Flygonial/The-Gryphon-Foam-Dart-Blaster/Gryphon Takedown/Magwell TKD/Magwell (Grip) TKD.stl

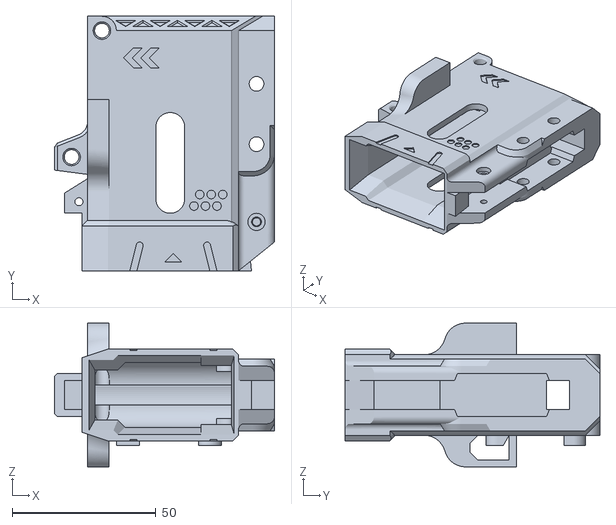
[picture p6: CAD file, 2022-05-22]
Gryphon Takedown/Magwell TKD/Magwell (Grip) TKD.stl
76.5 x 88.5 x 50.0
