Flygonial/The-Gryphon-Foam-Dart-Blaster/Gryphon Takedown/Other TKD Components/Pusher TKD.stl

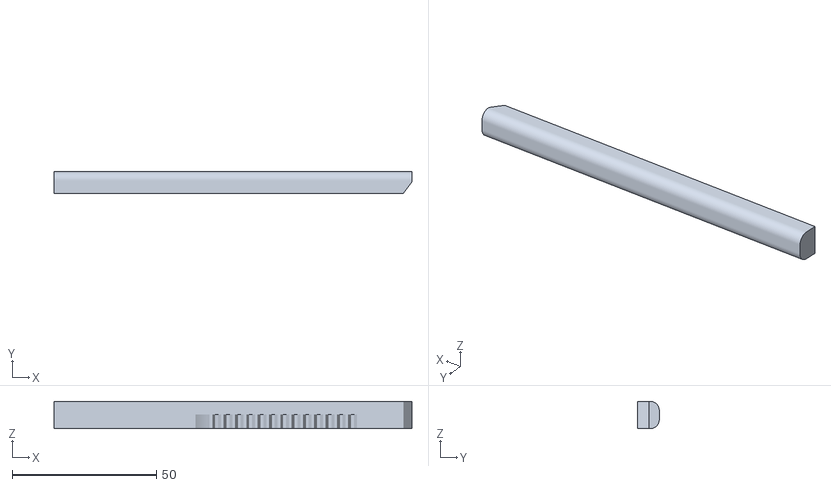
[picture p7: CAD file, 2022-05-22]
Gryphon Takedown/Other TKD Components/Pusher TKD.stl
124.1 x 7.50 x 9.50
