Flygonial/The-Gryphon-Foam-Dart-Blaster/Gryphon Takedown/Picatinny TKD/2S Bottom Picatinny TKD.stl

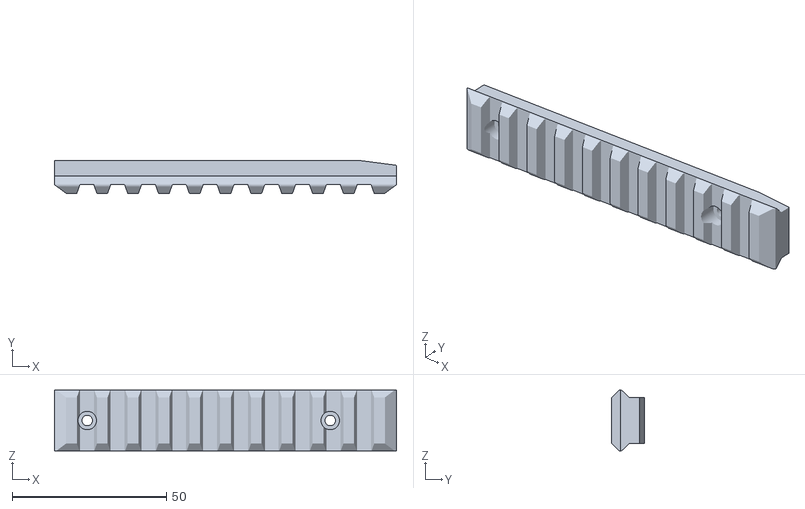
[picture p8: CAD file, 2021-01-16]
Gryphon Takedown/Picatinny TKD/2S Bottom Picatinny TKD.stl
111.0 x 10.6 x 19.8
