Flygonial/The-Gryphon-Foam-Dart-Blaster/Gryphon Takedown/TKD Battery Holders/Side Tray Door EXT (L).stl

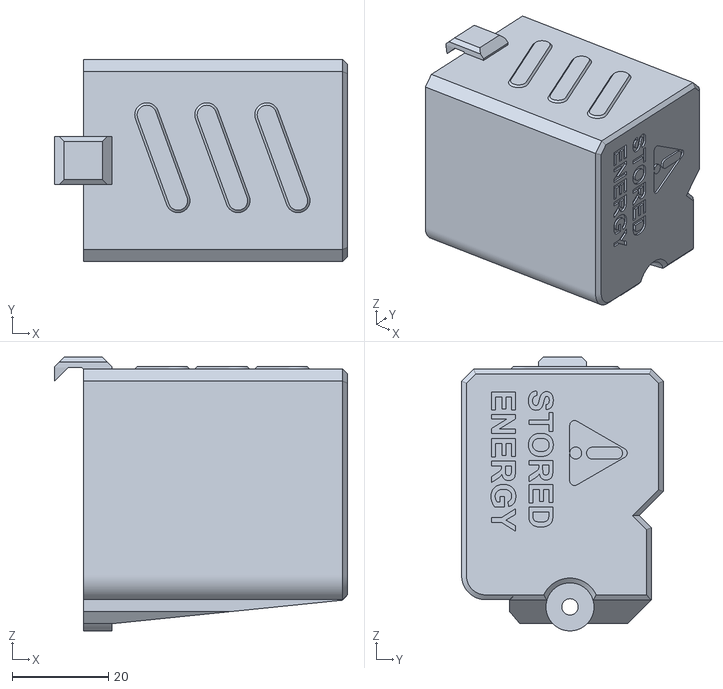
[picture p9: CAD file, 2022-05-22]
Gryphon Takedown/TKD Battery Holders/Side Tray Door EXT (L).stl
61.0 x 42.0 x 57.0
