Flygonial/The-Gryphon-Foam-Dart-Blaster/STLs/Accessories/FL Magwell Picatinny.stl

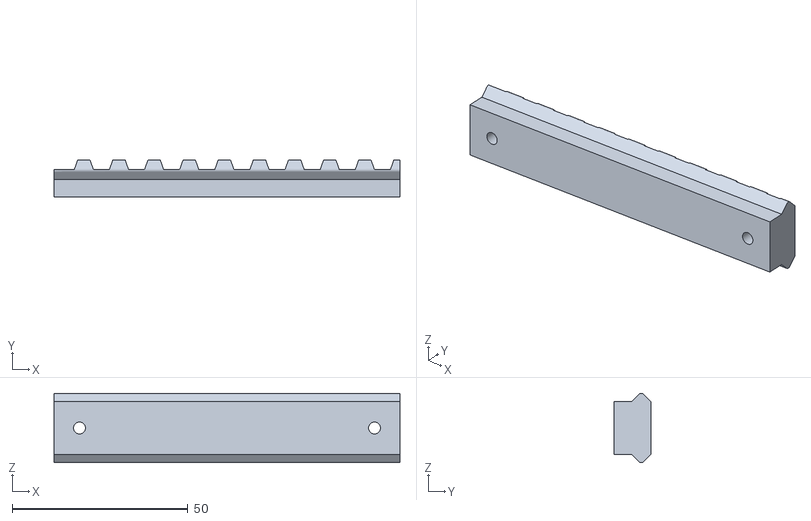
[picture p10: CAD file, 2022-05-16]
STLs/Accessories/FL Magwell Picatinny.stl
98.5 x 10.6 x 19.8
