Flygonial/The-Gryphon-Foam-Dart-Blaster/STLs/Battery Stock/Buffer Battery Stock/Buffer Tube V1.31.stl

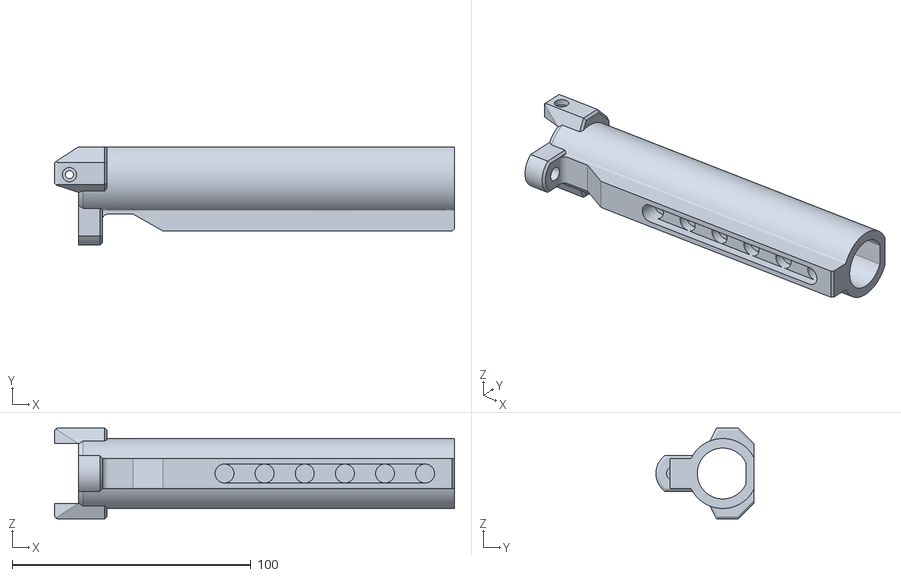
[picture p11: CAD file, 2022-08-07]
STLs/Battery Stock/Buffer Battery Stock/Buffer Tube V1.31.stl
167.5 x 41.2 x 38.0
