Flygonial/The-Gryphon-Foam-Dart-Blaster/STLs/Battery Stock/Default Stock/Tray Door Buttplate.stl

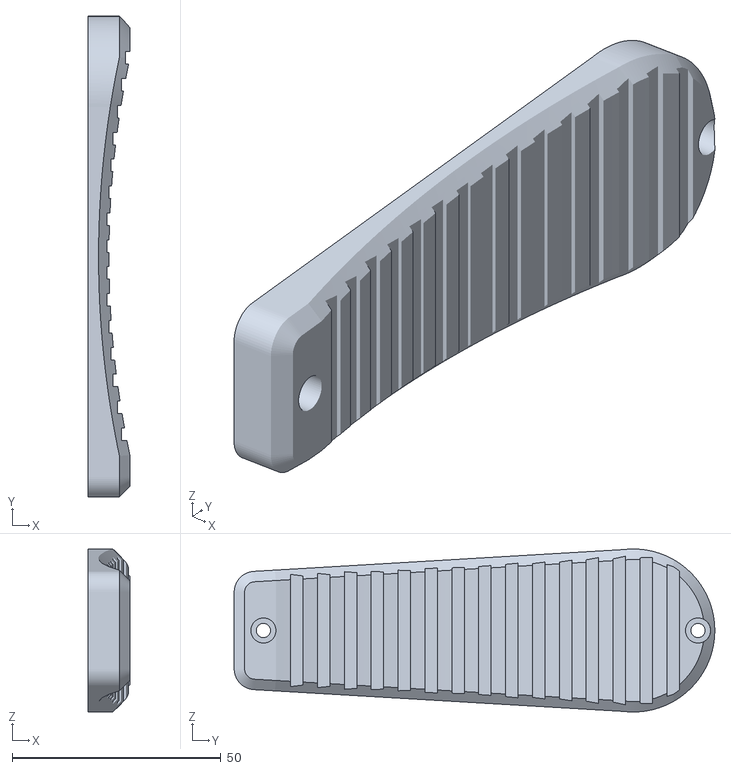
[picture p12: CAD file, 2019-05-02]
STLs/Battery Stock/Default Stock/Tray Door Buttplate.stl
10.0 x 115.0 x 39.0
