Flygonial/The-Gryphon-Foam-Dart-Blaster/STLs/Battery Stock/EXPD Stock/EXPD Battery Stock (KS + VML) (Imperial).stl

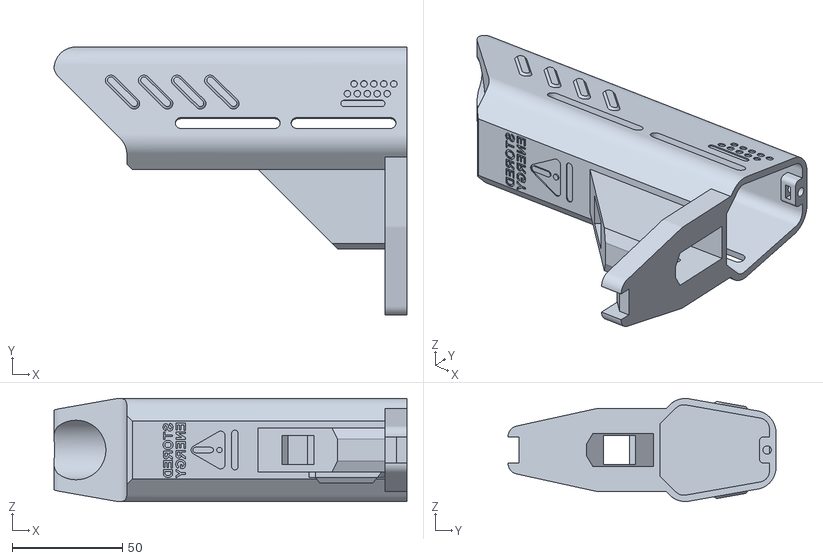
[picture p13: CAD file, 2020-06-11]
STLs/Battery Stock/EXPD Stock/EXPD Battery Stock (KS + VML) (Imperial).stl
160.0 x 121.5 x 46.7
