Flygonial/The-Gryphon-Foam-Dart-Blaster/STLs/Battery Stock/Imperial/Stock Cap (Attach) (Imperial).stl

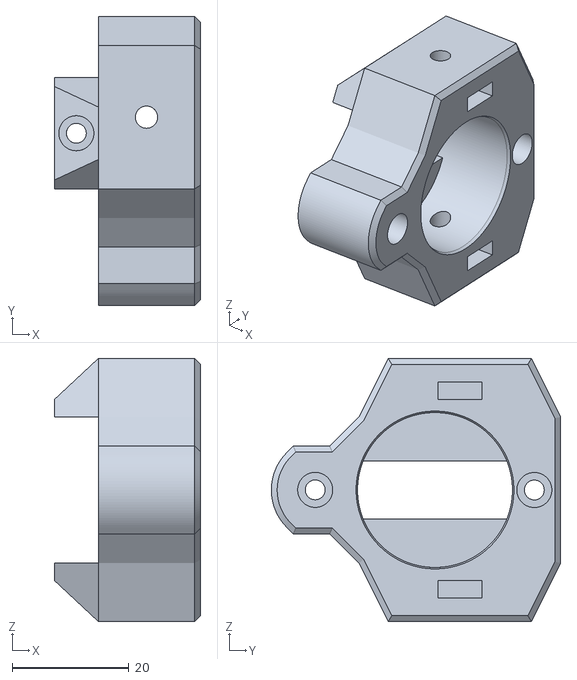
[picture p14: CAD file, 2020-06-11]
STLs/Battery Stock/Imperial/Stock Cap (Attach) (Imperial).stl
25.0 x 49.5 x 45.0
