Flygonial/The-Gryphon-Foam-Dart-Blaster/STLs/Battery Stock/Side Battery Tray/Side Battery Tray (R).stl

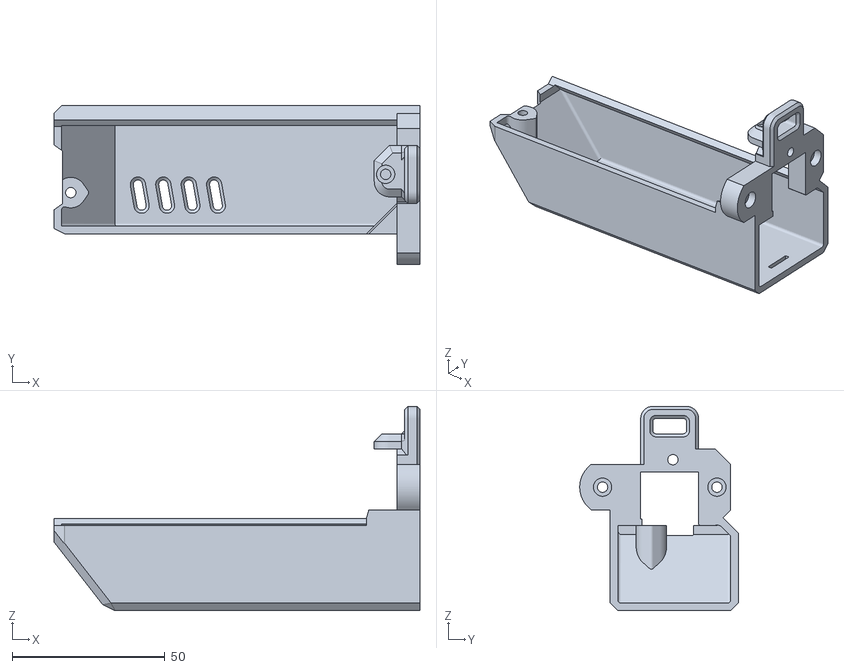
[picture p15: CAD file, 2022-05-16]
STLs/Battery Stock/Side Battery Tray/Side Battery Tray (R).stl
120.0 x 52.0 x 67.0
