Flygonial/The-Gryphon-Foam-Dart-Blaster/STLs/Flywheel Cage/14.5mm Bore FWC/2-Stage FWC (14.5)/40mm (14.5)/2S 40mm FWC (14.5).stl

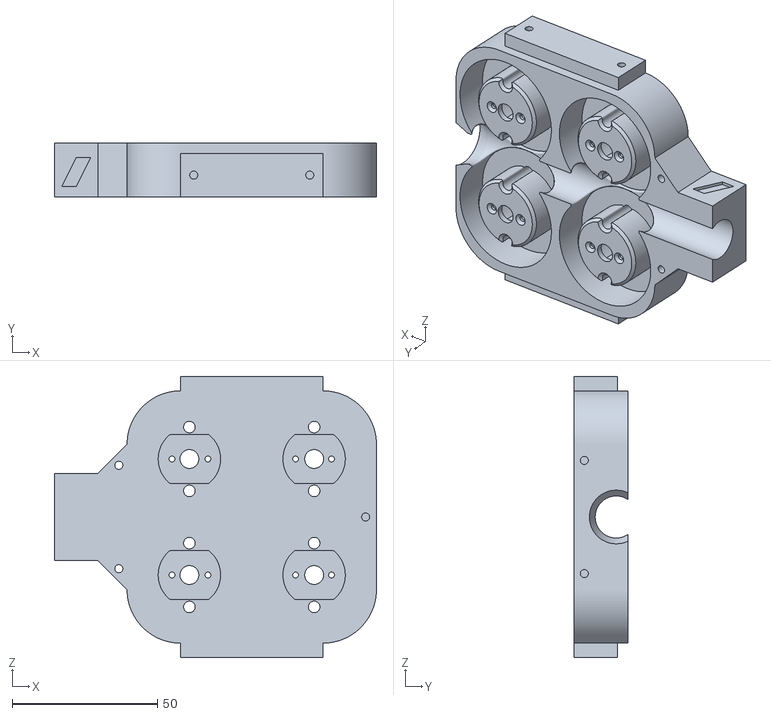
[picture p16: CAD file, 2020-06-11]
STLs/Flywheel Cage/14.5mm Bore FWC/2-Stage FWC (14.5)/40mm (14.5)/2S 40mm FWC (14.5).stl
111.0 x 18.5 x 97.0
