Flygonial/The-Gryphon-Foam-Dart-Blaster/STLs/Flywheel Cage/14.5mm Bore FWC/2-Stage FWC (14.5)/41.5mm (14.5)/2S 41.5mm FW Cover (14.5).stl

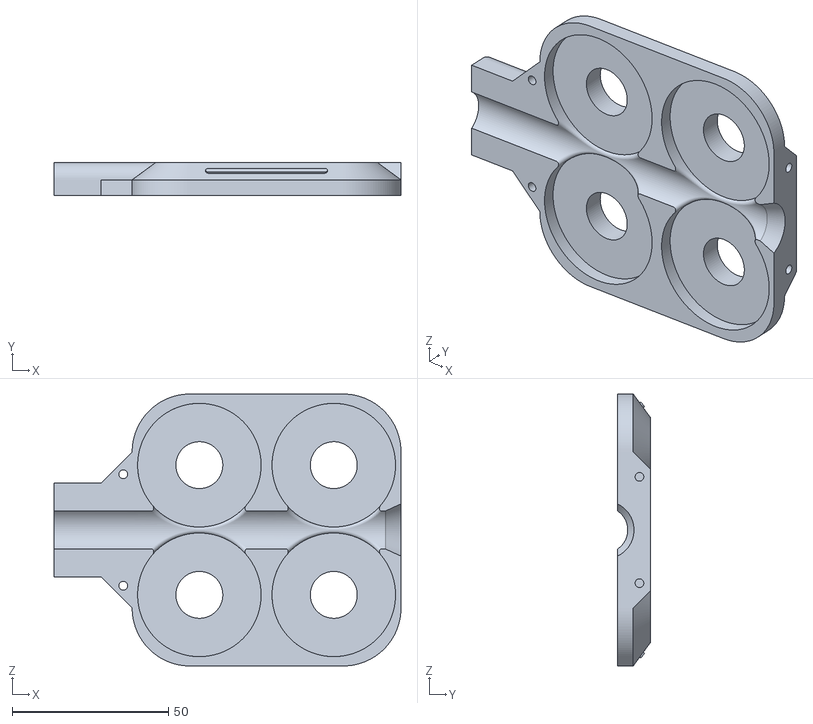
[picture p17: CAD file, 2020-06-11]
STLs/Flywheel Cage/14.5mm Bore FWC/2-Stage FWC (14.5)/41.5mm (14.5)/2S 41.5mm FW Cover (14.5).stl
111.0 x 10.5 x 87.0
