Flygonial/The-Gryphon-Foam-Dart-Blaster/STLs/Flywheel Cage/14.5mm Bore FWC/40mm (14.5)/40mm FW Cover (14.5).stl

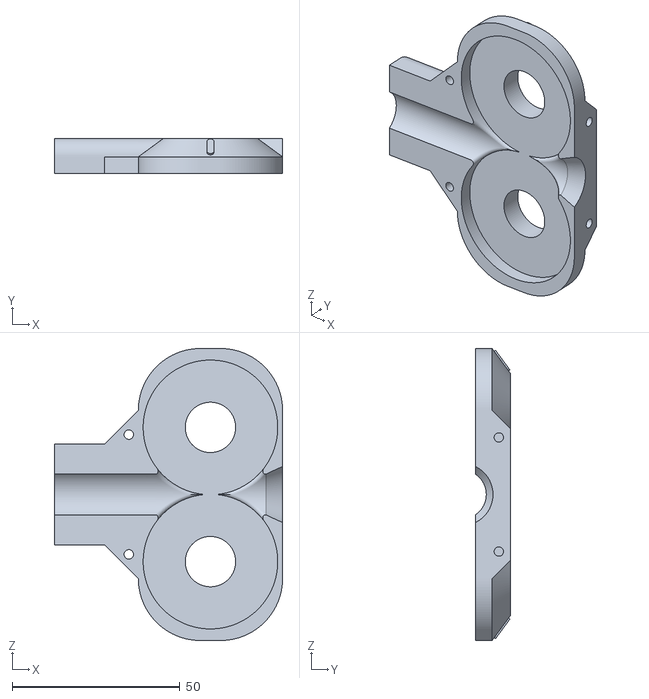
[picture p18: CAD file, 2022-05-16]
STLs/Flywheel Cage/14.5mm Bore FWC/40mm (14.5)/40mm FW Cover (14.5).stl
68.0 x 10.5 x 87.0
