Flygonial/The-Gryphon-Foam-Dart-Blaster/STLs/Flywheel Cage/14.5mm Bore FWC/42.5mm (14.5)/42.5mm FWC (14.5).stl

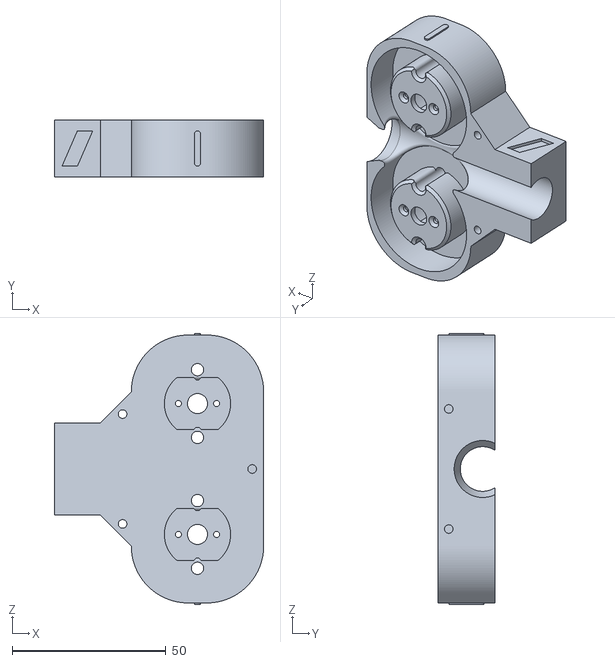
[picture p19: CAD file, 2022-05-17]
STLs/Flywheel Cage/14.5mm Bore FWC/42.5mm (14.5)/42.5mm FWC (14.5).stl
68.0 x 18.5 x 88.0
