Flygonial/The-Gryphon-Foam-Dart-Blaster/STLs/Flywheel Cage/2-Stage FWC/2-Stage Picatinny/2S + FL Top Picatinny (Mid).stl

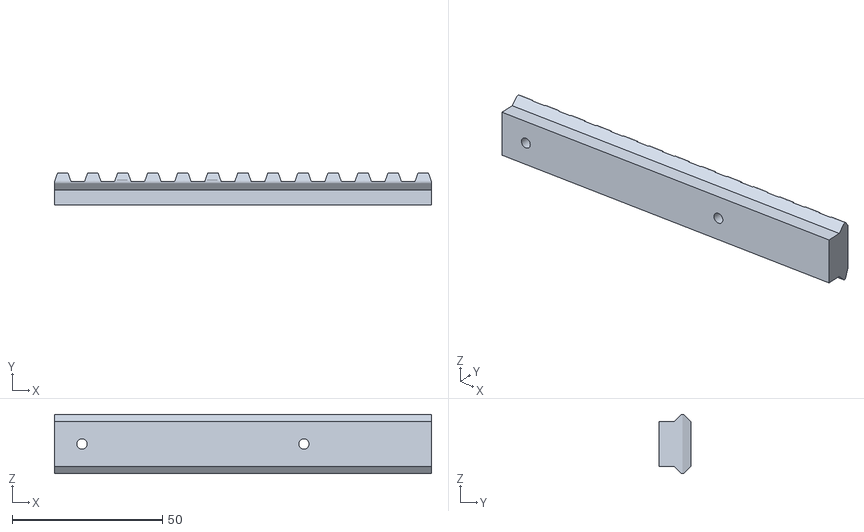
[picture p20: CAD file, 2020-02-08]
STLs/Flywheel Cage/2-Stage FWC/2-Stage Picatinny/2S + FL Top Picatinny (Mid).stl
125.5 x 10.6 x 19.8
