Flygonial/The-Gryphon-Foam-Dart-Blaster/STLs/Flywheel Cage/2-Stage FWC/2S Motor Cover.stl

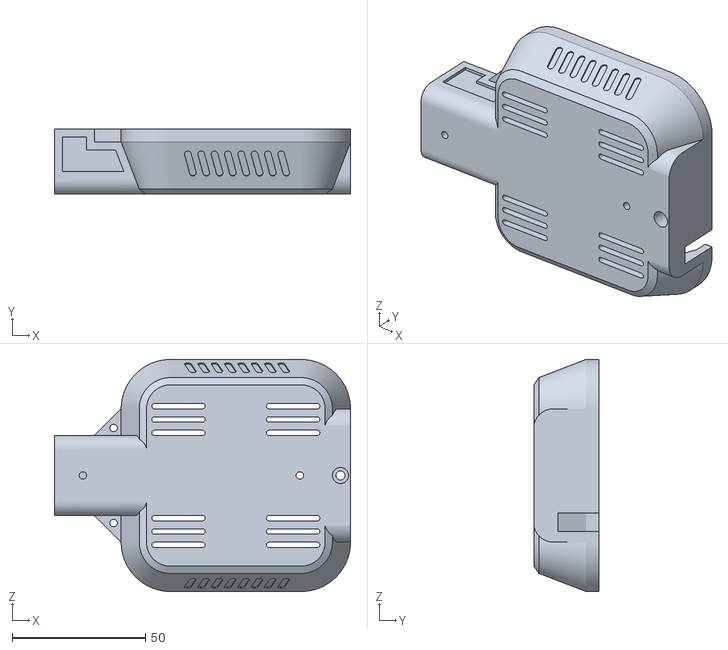
[picture p21: CAD file, 2020-01-27]
STLs/Flywheel Cage/2-Stage FWC/2S Motor Cover.stl
111.0 x 24.5 x 87.0
