Flygonial/The-Gryphon-Foam-Dart-Blaster/STLs/Grip/Left Panel WD.stl

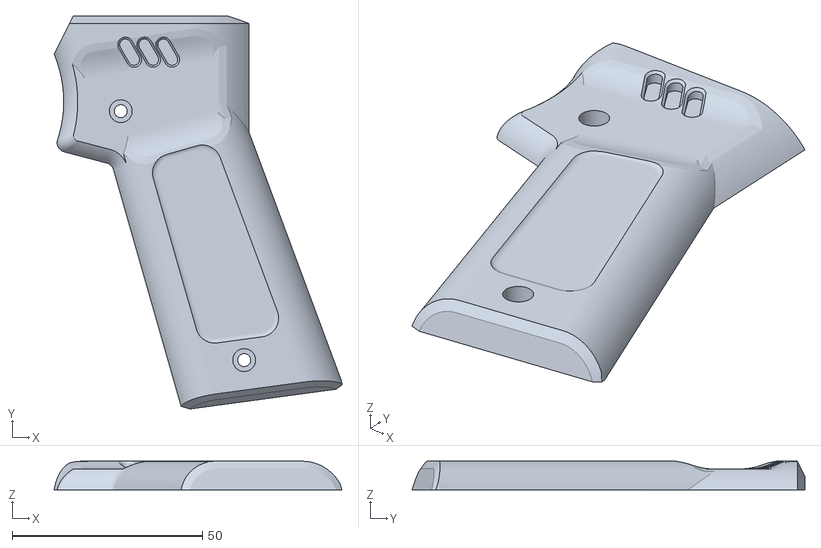
[picture p22: CAD file, 2022-05-16]
STLs/Grip/Left Panel WD.stl
75.6 x 103.2 x 7.50
