Flygonial/The-Gryphon-Foam-Dart-Blaster/STLs/Magwell/Full-Length/FL Magwell (Grip).stl

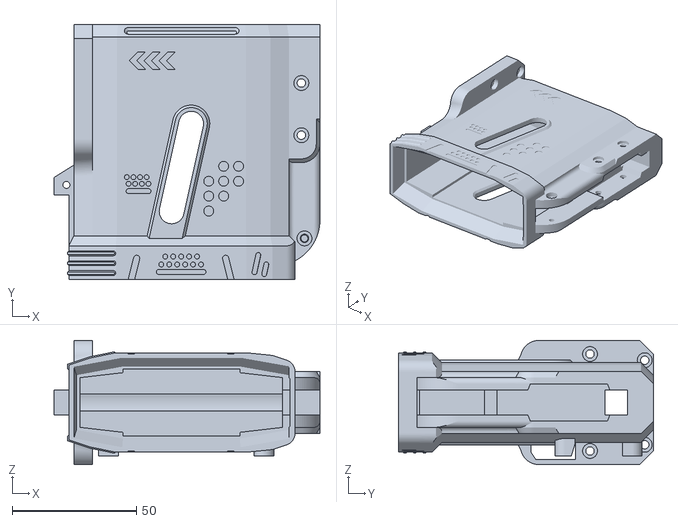
[picture p23: CAD file, 2022-05-16]
STLs/Magwell/Full-Length/FL Magwell (Grip).stl
107.0 x 102.5 x 50.0
