Flygonial/The-Gryphon-Foam-Dart-Blaster/STLs/Magwell/Half-Length/Kathanha/Kathanha Magwell (Grip).stl

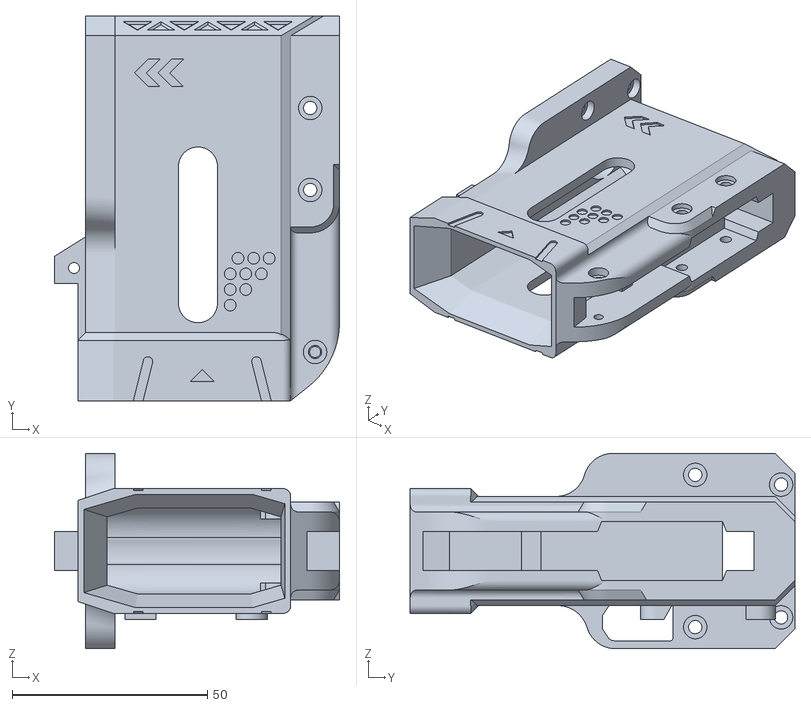
[picture p24: CAD file, 2022-05-16]
STLs/Magwell/Half-Length/Kathanha/Kathanha Magwell (Grip).stl
73.0 x 98.5 x 50.0
