Flygonial/The-Gryphon-Foam-Dart-Blaster/STLs/Magwell/Half-Length/Talon/Magwell.stl

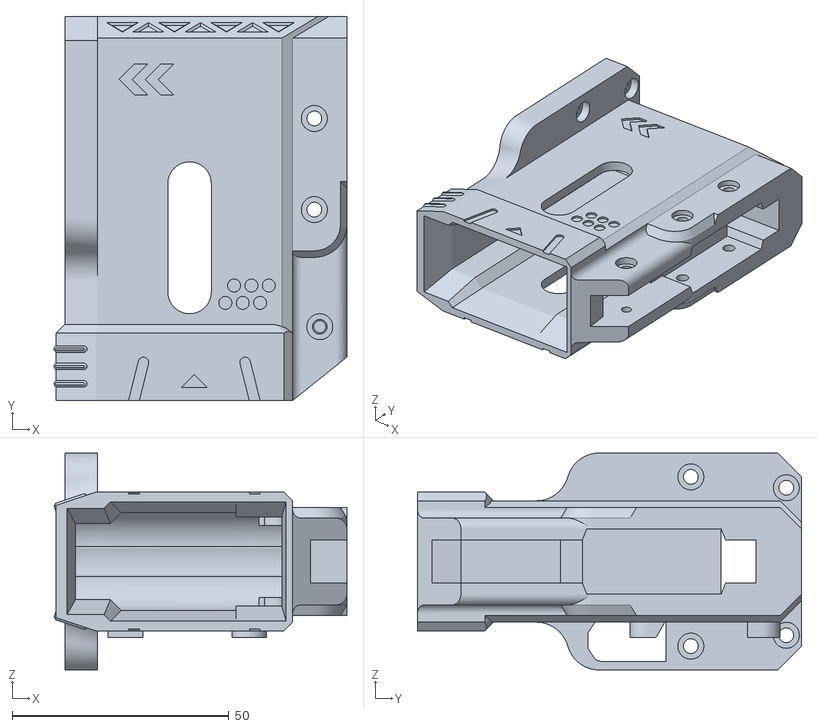
[picture p25: CAD file, 2022-05-16]
STLs/Magwell/Half-Length/Talon/Magwell.stl
67.5 x 88.5 x 50.0
