Flygonial/The-Gryphon-Foam-Dart-Blaster/STLs/Magwell/Half-Length/Wire Run.stl

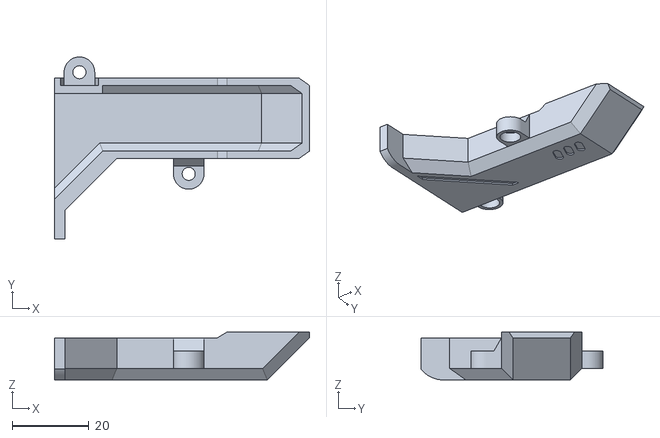
[picture p26: CAD file, 2019-08-03]
STLs/Magwell/Half-Length/Wire Run.stl
66.5 x 47.5 x 12.5
