Flygonial/The-Gryphon-Foam-Dart-Blaster/STLs/Magwell/Magwell Joint.stl

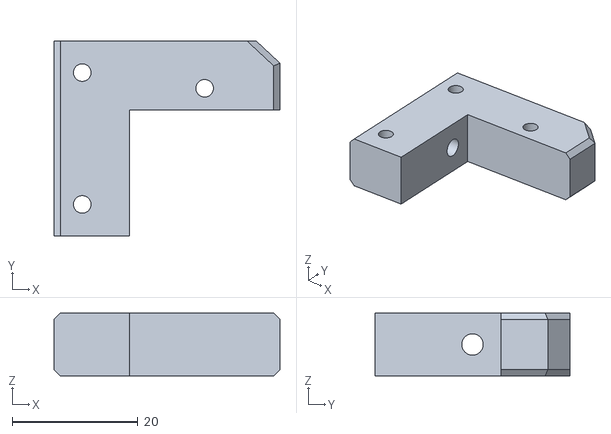
[picture p27: CAD file, 2019-04-22]
STLs/Magwell/Magwell Joint.stl
36.0 x 31.0 x 10.0
