Flygonial/The-Gryphon-Foam-Dart-Blaster/STLs/Pusher Mechanism/Mech Cover.stl

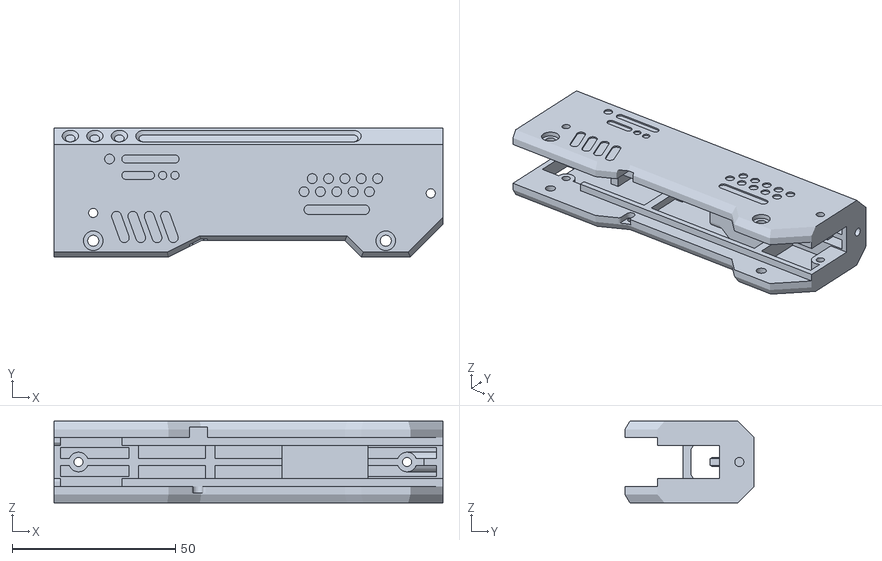
[picture p28: CAD file, 2023-03-14]
STLs/Pusher Mechanism/Mech Cover.stl
119.0 x 39.5 x 25.0
