Flygonial/The-Gryphon-Foam-Dart-Blaster/Gryphon Takedown/Magwell TKD/Wire Run EXPD TKD.stl

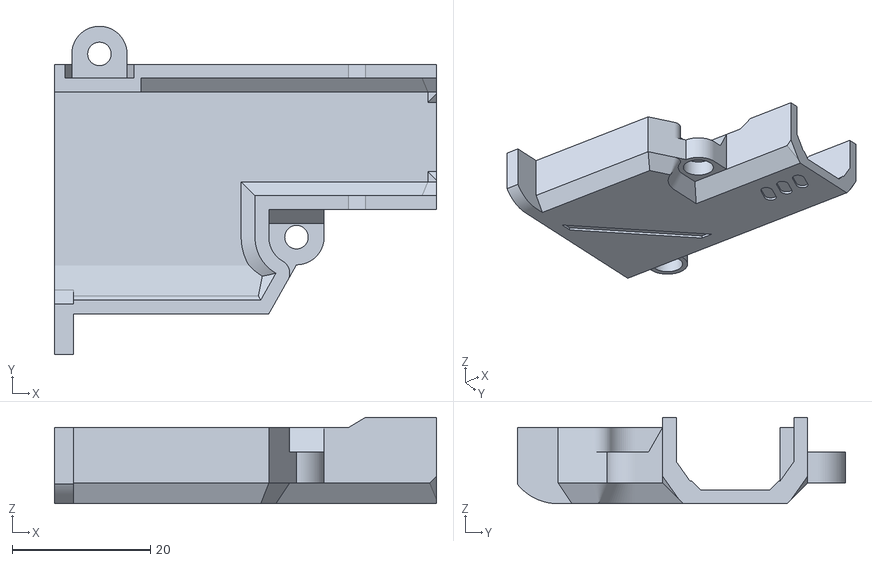
[picture p29: CAD file, 2022-05-22]
Gryphon Takedown/Magwell TKD/Wire Run EXPD TKD.stl
55.2 x 47.5 x 12.5
