Flygonial/The-Gryphon-Foam-Dart-Blaster/Gryphon Takedown/Picatinny TKD/Bottom Picatinny TKD.stl

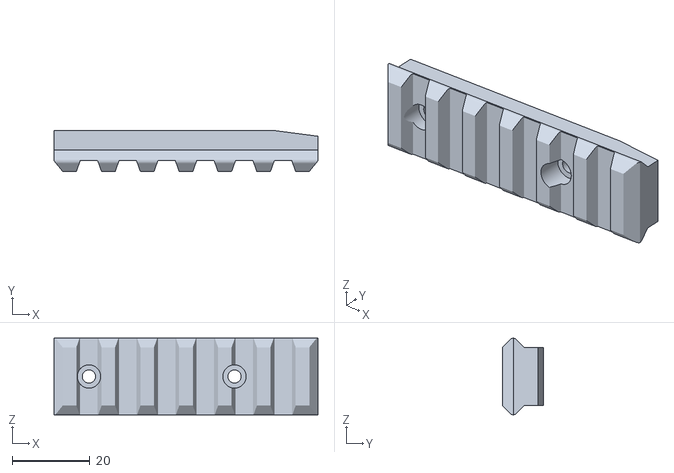
[picture p30: CAD file, 2021-01-16]
Gryphon Takedown/Picatinny TKD/Bottom Picatinny TKD.stl
68.0 x 10.6 x 19.8
