Flygonial/The-Gryphon-Foam-Dart-Blaster/Gryphon Takedown/TKD Battery Holders/Stock Cap (L) (Imperial).stl

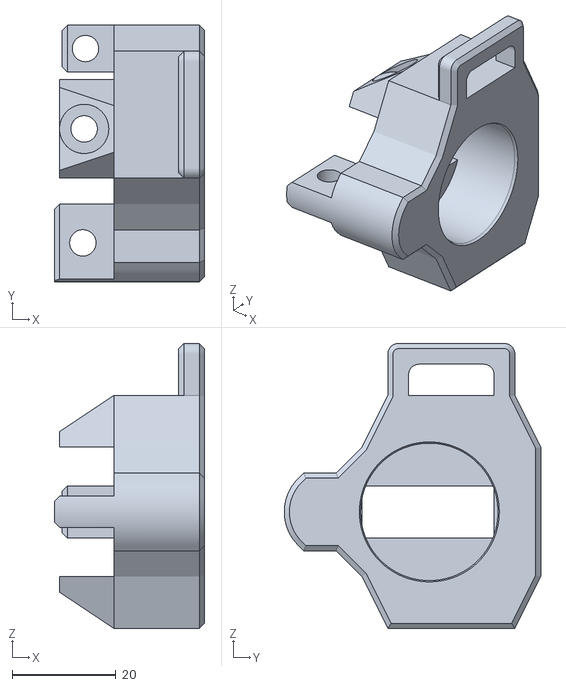
[picture p31: CAD file, 2022-05-22]
Gryphon Takedown/TKD Battery Holders/Stock Cap (L) (Imperial).stl
29.0 x 49.5 x 55.0
