Flygonial/The-Gryphon-Foam-Dart-Blaster/STLs/Accessories/1S FWC Picatinny.stl

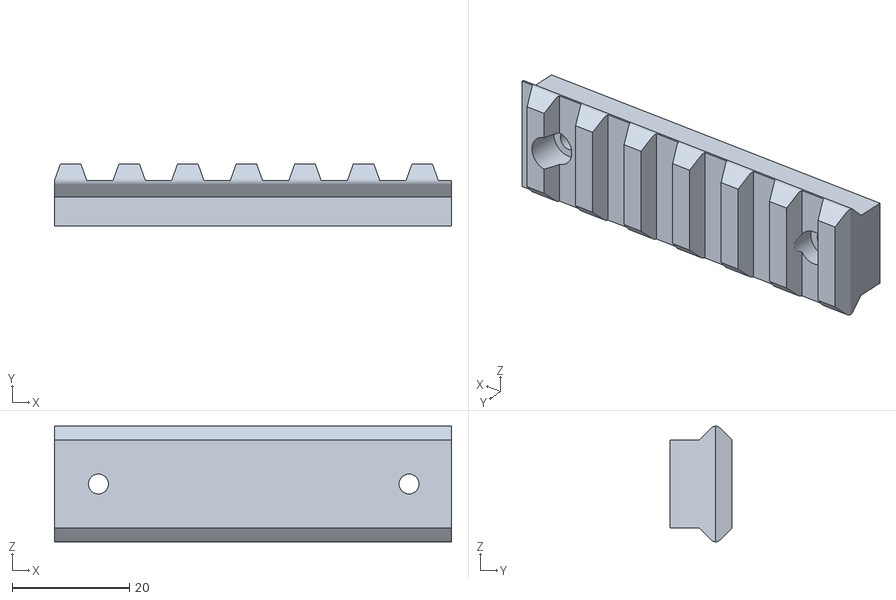
[picture p32: CAD file, 2022-05-16]
STLs/Accessories/1S FWC Picatinny.stl
67.8 x 10.6 x 19.8
