Flygonial/The-Gryphon-Foam-Dart-Blaster/STLs/Battery Stock/Buffer Battery Stock/Buffer Tube Top Mount.stl

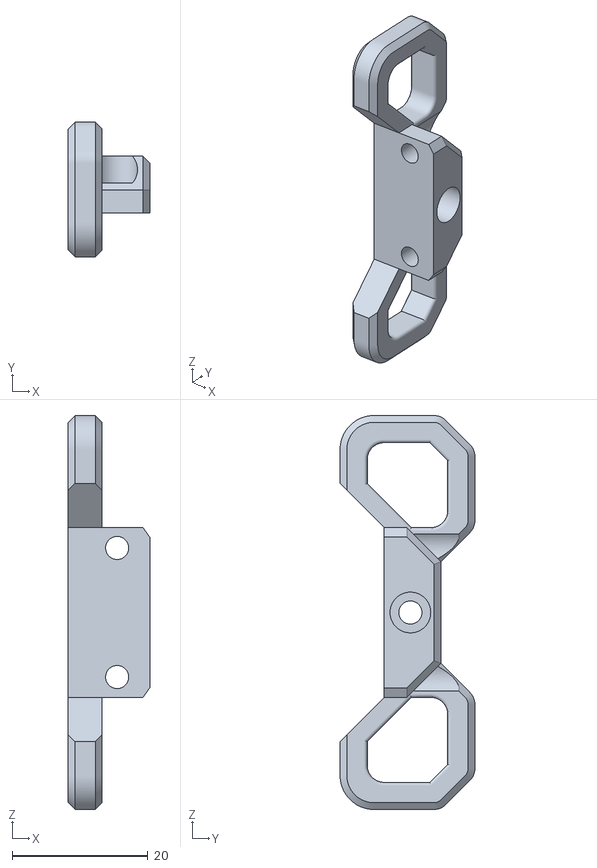
[picture p33: CAD file, 2022-08-07]
STLs/Battery Stock/Buffer Battery Stock/Buffer Tube Top Mount.stl
12.0 x 19.8 x 58.0
