Flygonial/The-Gryphon-Foam-Dart-Blaster/STLs/Battery Stock/Default Stock/Battery Stock (KS + VM).stl

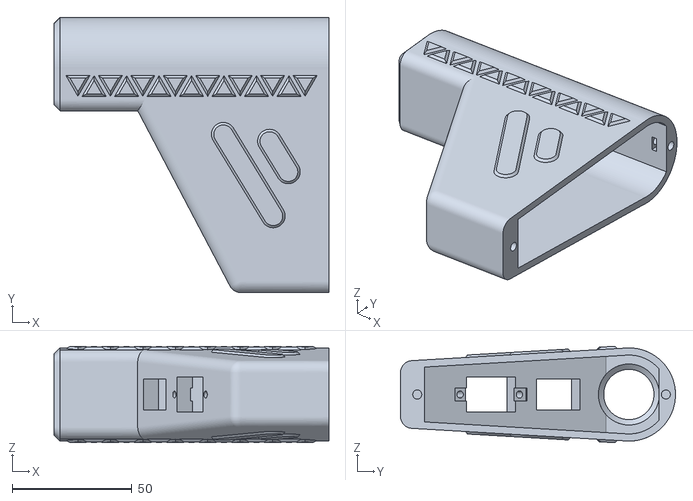
[picture p34: CAD file, 2019-04-22]
STLs/Battery Stock/Default Stock/Battery Stock (KS + VM).stl
115.0 x 115.0 x 40.3
